nusense/watson4x4_mqtt/secrets.h

const char* ssid        = "<wifi-ssid>";
const char* password    = "<wifi-password>";
const char* mqtt_server = "beaglebone0.local";
int         mqtt_port   = 1883;
const char* mqtt_user   = "<mqtt-user>";
const char* mqtt_pass   = "<mqtt-password>";
